jfeiber/buzzer-embedded/buzzer/BuzzerFSMCallbacks.h

/*
  File:
  BuzzerFSMCallbacks.h

  Description:
  Contains all the functions that represent the work a state needs to perform. Called by
  BuzzerFSM::DoState.
*/

#ifndef BUZZERFSMCALLBACKS_H
#define BUZZERFSMCALLBACKS_H

#include "Helpers.h"
#include "Pins.h"

#define PARTY_AVAIL_FIELD "p_a"
#define PARTY_NAME_FIELD "n"
#define PARTY_WAIT_TIME_FIELD "t"
#define PARTY_ID_FIELD "id"
#define BUZZER_NAME_FIELD "bn"
#define IS_ACTIVE_FIELD "i_a"
#define BUZZ_FIELD "b"
#define IS_BUZZER_REGISTERED_FIELD "i_reg"
#define ERROR_STATUS_FIELD "e"
#define ERROR_MESSAGE_FIELD "e_msg"


// Used in states that are meant to be repeated multiple times without error. This int and the
// corresponding macro allow a state to keep track of how many times it has errored. If a state
// doesn't normally repeat and is only meant to be run once before transition, we can just return
// repeat and check if num_iterations_in_state is greater than MAX_RETRIES. States that are meant to
// be run more than once can't do that, hence this int and macro. This is a little janky as this
// probably should be something that BuzzerFSM handles but I elected to do this as a band-aid as
// to not add additional complications to BuzzerFSM when only a few states need to use this.
static int num_iterations_in_error = 0;
#define CHECK_ERR_IN_INTERATION(err, val_when_err) \
  if (err == val_when_err) { \
      if (num_iterations_in_error >= MAX_RETRIES) return ERROR; \
      num_iterations_in_error++; \
      return REPEAT; \
  } \
  num_iterations_in_error = 0; \

int InitFunc(unsigned long state_start_time, int num_iterations_in_state);
int BuzzFunc(unsigned long state_start_time, int num_iterations_in_state);
int InitFonaShieldFunc(unsigned long state_start_time, int num_iterations_in_state);
int InitGPRSFunc(unsigned long state_start_time, int num_iterations_in_state);
int GetBuzzerNameFunc(unsigned long state_start_time, int num_iterations_in_state);
int IdleFunc(unsigned long state_start_time, int num_iterations_in_state);
int CheckBuzzerRegFunc(unsigned long state_start_time, int num_iterations_in_state);
int WaitBuzzerRegFunc(unsigned long state_start_time, int num_iterations_in_state);
static int IsBuzzerRegistered(bool *is_buzzer_registered);
int GetAvailPartyFunc(unsigned long state_start_time, int num_iterations_in_state);
static int APIPOSTBuzzerName(FlashStrPtr api_endpoint, char *rep_buf, int rep_buf_len, bool is_buzzing);
int AcceptAvailPartyFunc(unsigned long state_start_time, int num_iterations_in_state);
int HeartbeatFunc(unsigned long state_start_time, int num_iterations_in_state);
int ShutdownFunc(unsigned long state_start_time, int num_iterations_in_state);
int SleepFunc(unsigned long state_start_time, int num_iterations_in_state);
int WakeupFunc(unsigned long state_start_time, int num_iterations_in_state);
int ChargeFunc(unsigned long state_start_time, int num_iterations_in_state);
int FatalErrorFunc(unsigned long state_start_time, int num_iterations_in_state);
int LowCellReceptionFunc(unsigned long state_start_time, int num_iterations_in_state);
static void UpdateBatteryPercentage(int row, int num_iterations_in_state);

#endif
