jfeiber/buzzer-embedded/buzzer/Globals.h

/*
  File:
  Globals.h

  Description:
  Contains all the global variables/defines used by Buzzer.
*/

#ifndef GLOBALS_H
#define GLOBALS_H

#include <SoftwareSerial.h>
#include "BuzzerFSM.h"
#include "FonaShield.h"
#include "SSD1306Ascii.h"
#include "SSD1306AsciiAvrI2c.h"
#include "EEPROMReadWrite.h"

#define MAX_RETRIES 10
#define BUF_LENGTH_LARGE 90
#define BUF_LENGTH_MEDIUM 64
#define BUF_LENGTH_SMALL 32
#define NO_PARTY -1
#define LOW_SIGNAL_THRESHOLD 5

extern BuzzerFSM buzzer_fsm;
extern SoftwareSerial fona_serial;
extern FonaShield fona_shield;
extern SSD1306AsciiAvrI2c oled;
enum ret_vals {SUCCESS, ERROR, REPEAT, TIMEOUT};
extern EEPROMData eeprom_data;
extern short batt_percentage;
extern bool has_system_been_initialized;
extern unsigned long button_press_start;
extern bool usb_cabled_plugged_in;

#endif
