jfeiber/buzzer-embedded/buzzer/Version.h

/*
  File:
  Version.h

  Description:
  Provides a way to change the build for various versions of PCBs.
 */

#ifndef VERSION_H
#define VERSION_H

enum pcb_versions {V1, V2, JANKBOARD};

#define BOARD_TYPE V2

#endif
