jfeiber/buzzer-embedded/buzzer/LPF.h

/*
  File:
  LPF.h

  Description:
  Methods for implementing a low pass filter.
  Implementation from :  http://webcache.googleusercontent.com/search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
*/

#ifndef LPF_H
#define LPF_H

// Corresponds to how much weight battery voltage samples are given in the filter. A higher
// shift here corresponds to lower weight.
#define LPF_FILTER_SHIFT 7

static signed long filter = 0;

inline void seed_lpf(int seed_val) {
  filter = seed_val << LPF_FILTER_SHIFT;
}

inline void add_val_to_lpf(int val_to_add) {
  filter = filter - (filter >> LPF_FILTER_SHIFT) + val_to_add;
}

inline signed long get_curr_lpf_val() {
  return filter >> LPF_FILTER_SHIFT;
}

#endif
